martinhol221/SIM800C_ESP8266/stl/PSA_ring_41.5.png

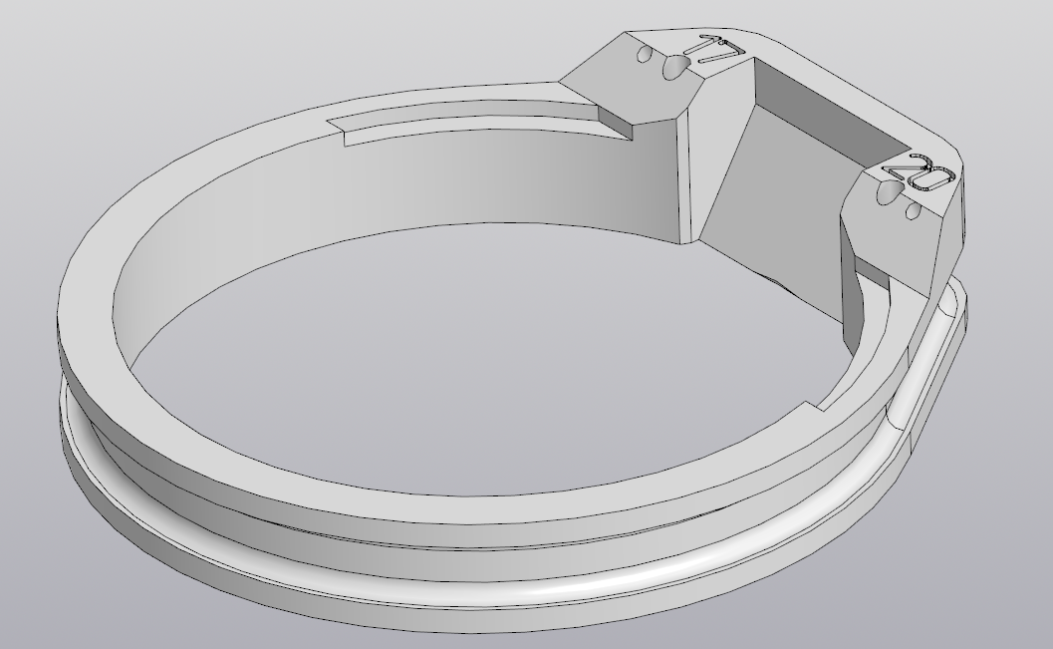
stl/PSA_ring_41.5.png
